ChartreuseK/Fennec6800_VTI/FennecVTI.kicad_sch

## KiCad design FennecVTI.kicad_sch (2023-05-26, an earlier design)

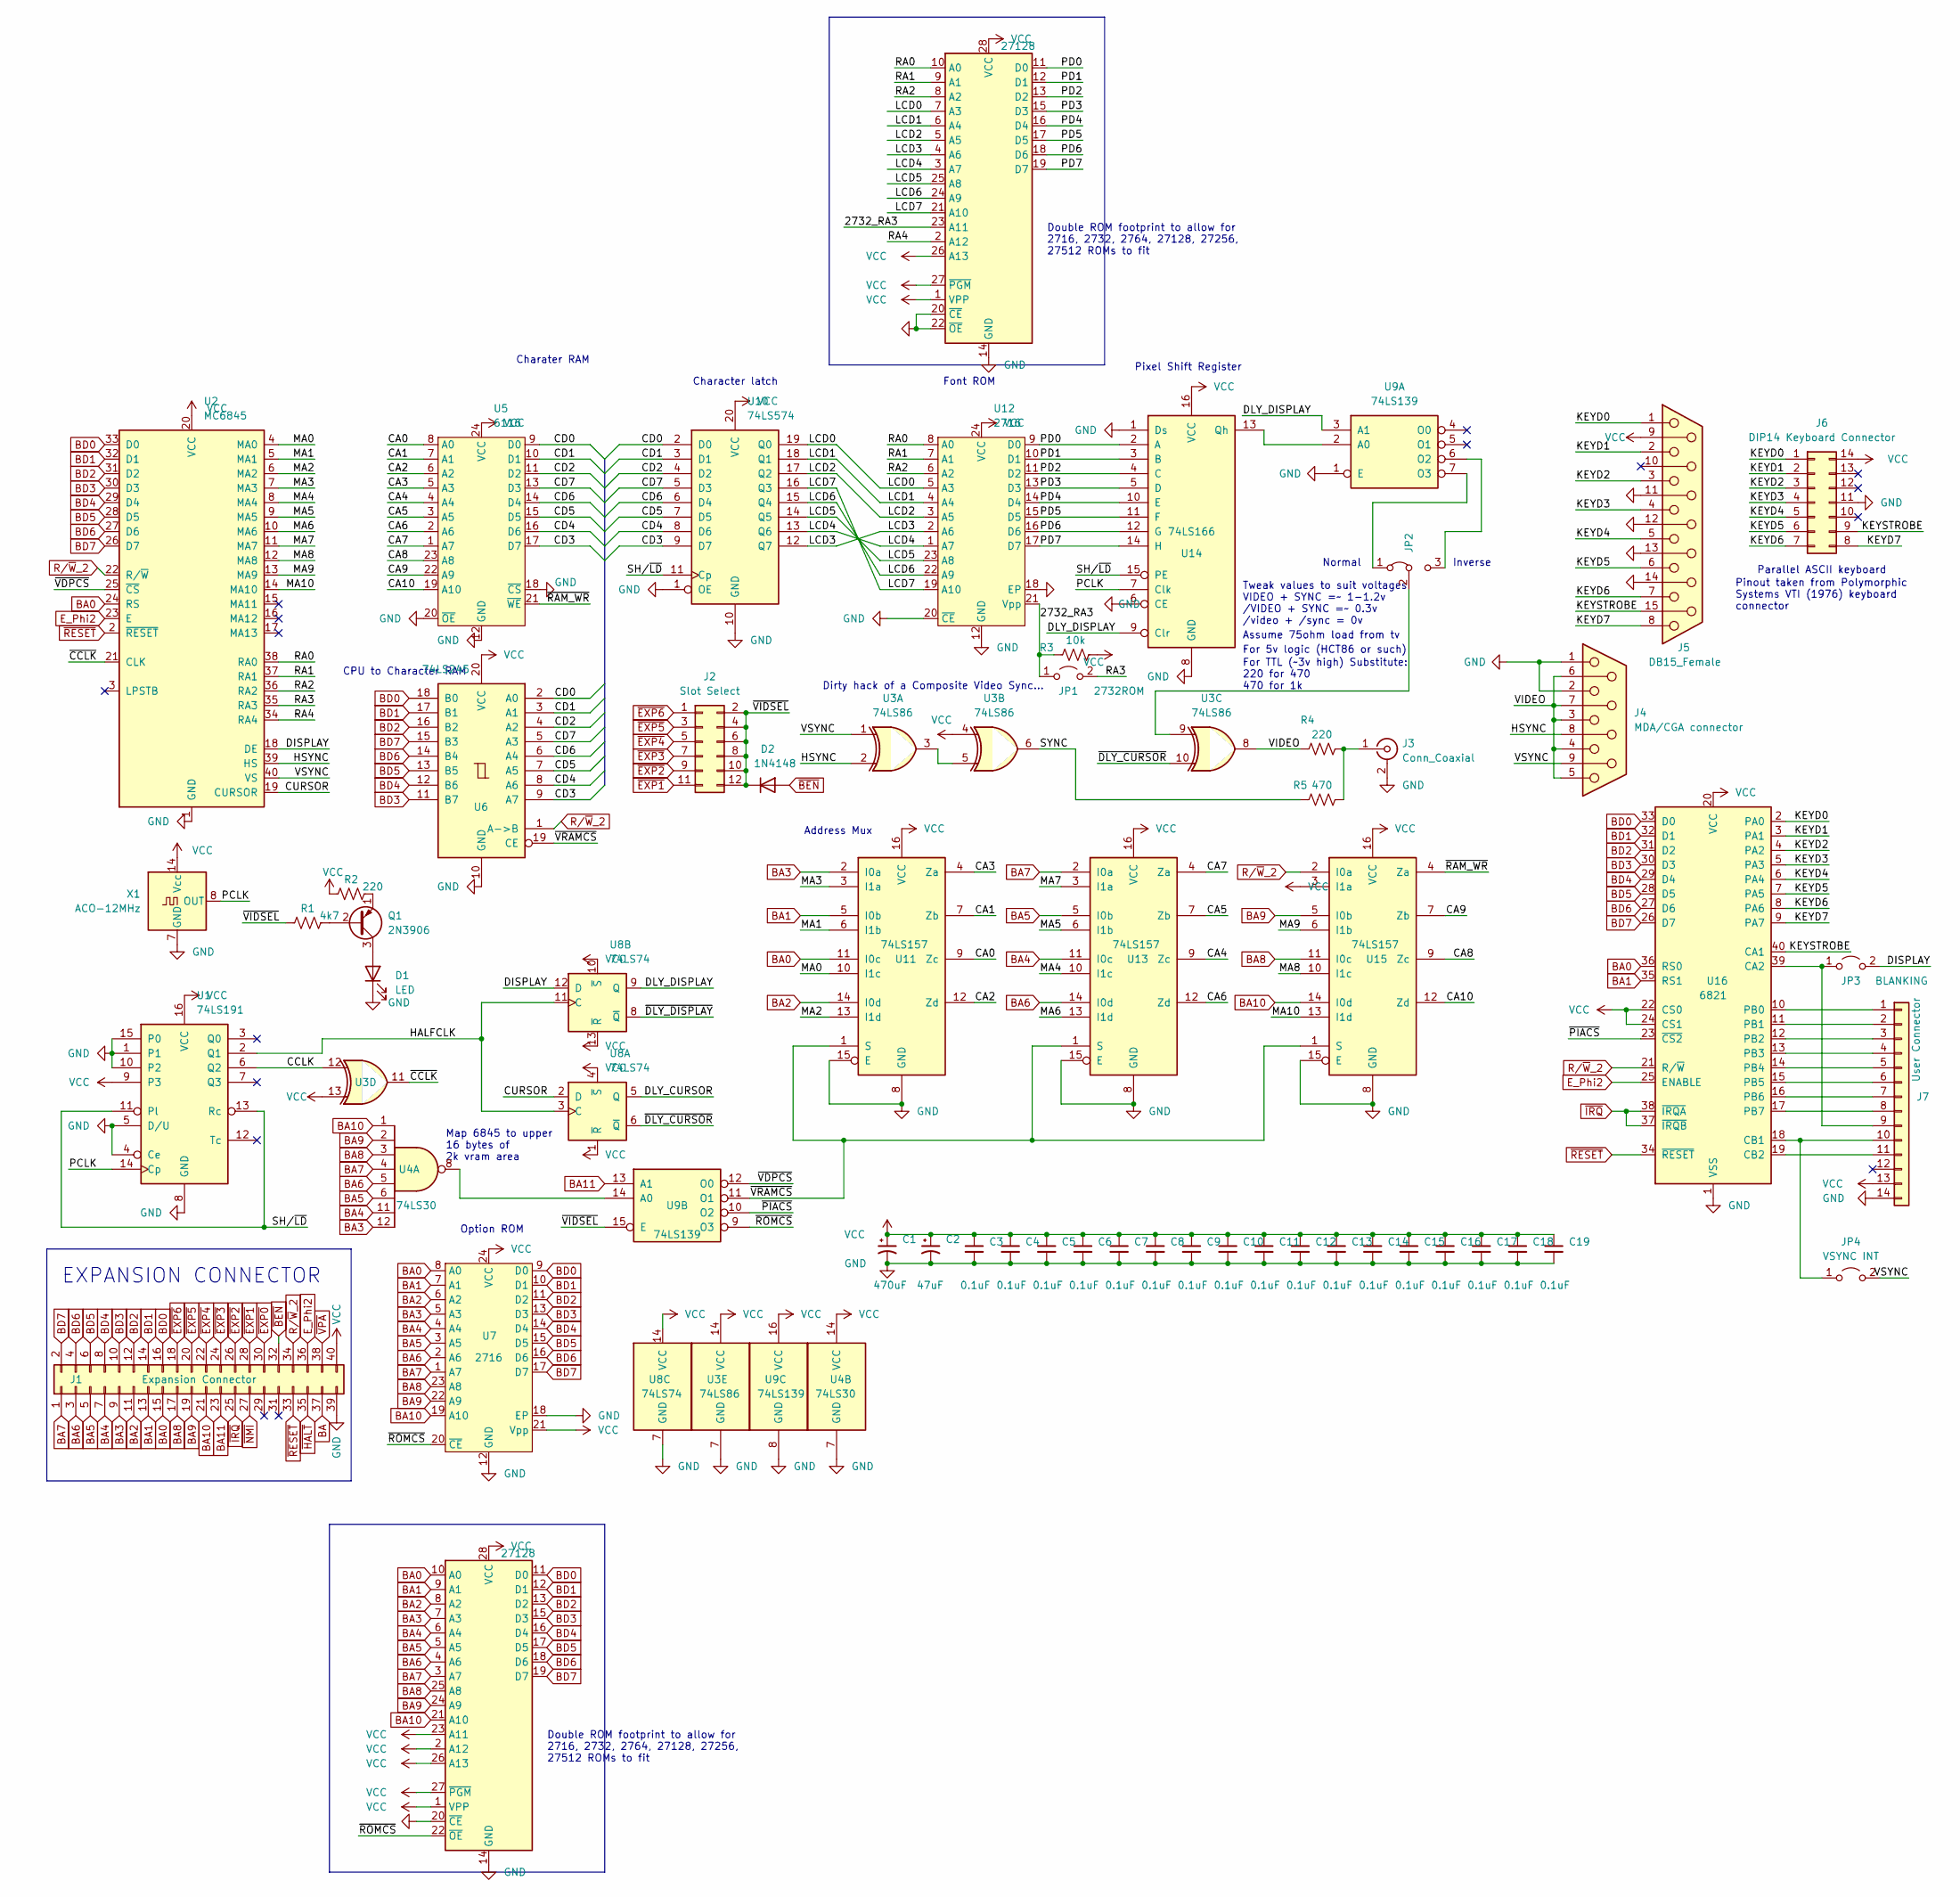
[picture p7: schematic FennecVTI.kicad_sch]

Parts:
C1: 470uF; CP_Radial_D8.0mm_P3.50mm
C2: 47uF; CP_Radial_D5.0mm_P2.00mm
C3, C4, C5, C6, C7, C8, C9, C10, C11, C12, C13, C14, C15, C16, C17, C18, C19: 0.1uF; C_Disc_D3.0mm_W1.6mm_P2.50mm
D1: LED; LED_D5.0mm
D2: 1N4148; D_DO-35_SOD27_P10.16mm_Horizontal
J1: Expansion Connector; PinHeader_2x20_P2.54mm_Vertical
J2: Slot Select; PinHeader_2x06_P2.54mm_Vertical
J3: Conn_Coaxial; RCA_RA_Switchcraft
J4: MDA/CGA connector; DSUB-9_Female_Horizontal_P2.77x2.84mm_EdgePinOffset7.70mm_H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
J5: DB15_Female; DSUB-15_Female_Horizontal_P2.77x2.84mm_EdgePinOffset7.70mm_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
J6: DIP14 Keyboard Connector; DIP-14_W7.62mm_Socket_LongPads
J7: User Connector; PinHeader_1x14_P2.54mm_Vertical
JP1: 2732ROM; PinHeader_1x02_P2.54mm_Vertical
JP2: Jumper_3_Bridged12; PinHeader_1x03_P2.54mm_Vertical
JP3: BLANKING; PinHeader_1x02_P2.54mm_Vertical
JP4: VSYNC INT; PinHeader_1x02_P2.54mm_Vertical
Q1: 2N3906; TO-92_Inline
R1: 4k7; R_Axial_DIN0207_L6.3mm_D2.5mm_P10.16mm_Horizontal
R2, R4: 220; R_Axial_DIN0207_L6.3mm_D2.5mm_P10.16mm_Horizontal
R3: 10k; R_Axial_DIN0207_L6.3mm_D2.5mm_P10.16mm_Horizontal
R5: 470; R_Axial_DIN0207_L6.3mm_D2.5mm_P10.16mm_Horizontal
U1: 74LS191; DIP-16 Copper Ref Pin 1 Mark
U2: MC6845; DIP-40 Copper Ref Pin 1
U3: 74LS86; DIP-14 Copper Ref Pin 1 Mark
U4: 74LS30; DIP-14 Copper Ref Pin 1 Mark
U5: 6116; DIP-24_W15.24mm_Socket_LongPads
U6: 74LS245; DIP-20 Copper Ref Pin 1 Mark
U7, U12: 2716; DIP-24_W15.24mm_Socket_LongPads
U8: 74LS74; DIP-14 Copper Ref Pin 1 Mark
U9: 74LS139; DIP-16 Copper Ref Pin 1 Mark
U10: 74LS574; DIP-20 Copper Ref Pin 1 Mark
U11, U13, U15: 74LS157; DIP-16 Copper Ref Pin 1 Mark
U14: 74LS166; DIP-16 Copper Ref Pin 1 Mark
U16: 6821; DIP-40 Copper Ref Pin 1
U70, U120: 27128; DIP-28_W15.24mm_Socket_LongPads
X1: ACO-12MHz; DIP-14-8 Crystal Silk Ref Pin 1 Outline

Connections:
2732_RA3: JP1.1 (A), R3.1, U12.21 (Vpp), U120.23 (A11)
BA: J1.37
BA0: J1.15, U2.24 (RS), U7.8 (A0), U11.11 (I0c), U16.36 (RS0), U70.10 (A0)
BA1: J1.13, U7.7 (A1), U11.5 (I0b), U16.35 (RS1), U70.9 (A1)
BA2: J1.11, U7.6 (A2), U11.14 (I0d), U70.8 (A2)
BA3: J1.9, U4.12, U7.5 (A3), U11.2 (I0a), U70.7 (A3)
BA4: J1.7, U4.11, U7.4 (A4), U13.11 (I0c), U70.6 (A4)
BA5: J1.5, U4.6, U7.3 (A5), U13.5 (I0b), U70.5 (A5)
BA6: J1.3, U4.5, U7.2 (A6), U13.14 (I0d), U70.4 (A6)
BA7: J1.1, U4.4, U7.1 (A7), U13.2 (I0a), U70.3 (A7)
BA8: J1.17, U4.3, U7.23 (A8), U15.11 (I0c), U70.25 (A8)
BA9: J1.19, U4.2, U7.22 (A9), U15.5 (I0b), U70.24 (A9)
BA10: J1.21, U4.1, U7.19 (A10), U15.14 (I0d), U70.21 (A10)
BA11: J1.23, U9.13 (A1)
BD0: J1.16, U2.33 (D0), U6.18 (B0), U7.9 (D0), U16.33 (D0), U70.11 (D0)
BD1: J1.14, U2.32 (D1), U6.17 (B1), U7.10 (D1), U16.32 (D1), U70.12 (D1)
BD2: J1.12, U2.31 (D2), U6.16 (B2), U7.11 (D2), U16.31 (D2), U70.13 (D2)
BD3: J1.10, U2.30 (D3), U6.11 (B7), U7.13 (D3), U16.30 (D3), U70.15 (D3)
BD4: J1.8, U2.29 (D4), U6.12 (B6), U7.14 (D4), U16.29 (D4), U70.16 (D4)
BD5: J1.6, U2.28 (D5), U6.13 (B5), U7.15 (D5), U16.28 (D5), U70.17 (D5)
BD6: J1.4, U2.27 (D6), U6.14 (B4), U7.16 (D6), U16.27 (D6), U70.18 (D6)
BD7: J1.2, U2.26 (D7), U6.15 (B3), U7.17 (D7), U16.26 (D7), U70.19 (D7)
CA0: U5.8 (A0), U11.9 (Zc)
CA1: U5.7 (A1), U11.7 (Zb)
CA2: U5.6 (A2), U11.12 (Zd)
CA3: U5.5 (A3), U11.4 (Za)
CA4: U5.4 (A4), U13.9 (Zc)
CA5: U5.3 (A5), U13.7 (Zb)
CA6: U5.2 (A6), U13.12 (Zd)
CA7: U5.1 (A7), U13.4 (Za)
CA8: U5.23 (A8), U15.9 (Zc)
CA9: U5.22 (A9), U15.7 (Zb)
CA10: U5.19 (A10), U15.12 (Zd)
CCLK: U1.6 (Q2), U3.12
CD0: U5.9 (D0), U6.2 (A0), U10.2 (D0)
CD1: U5.10 (D1), U6.3 (A1), U10.3 (D1)
CD2: U5.11 (D2), U6.4 (A2), U10.4 (D2)
CD3: U5.17 (D7), U6.9 (A7), U10.9 (D7)
CD4: U5.16 (D6), U6.8 (A6), U10.8 (D6)
CD5: U5.15 (D5), U6.7 (A5), U10.7 (D5)
CD6: U5.14 (D4), U6.6 (A4), U10.6 (D4)
CD7: U5.13 (D3), U6.5 (A3), U10.5 (D3)
CURSOR: U2.19 (CURSOR), U8.2 (D)
DISPLAY: JP3.2 (B), U2.18 (DE), U8.12 (D)
DLY_CURSOR: U8.5 (Q)
DLY_DISPLAY: U8.9 (Q), U9.3 (A1), U14.9 (Clr)
E_Phi2: J1.36, U2.23 (E), U16.25 (ENABLE)
GND: C1.2, C2.2, C3.2, C4.2, C5.2, C6.2, C7.2, C8.2, C9.2, C10.2, C11.2, C12.2, C13.2, C14.2, C15.2, C16.2, C17.2, C18.2, C19.2, D1.1 (K), J1.39, J3.2 (Ext), J4.1, J4.2, J5.11 (P111), J5.12, J5.13, J5.14, J6.11, J7.14, U1.1, U1.4 (Ce), U1.5 (D/U), U1.8 (GND), U1.10 (P2), U1.15 (P0), U2.1 (GND), U3.7 (GND), U4.7 (GND), U5.12 (GND), U5.18 (~CS), U5.20 (~OE), U6.10 (GND), U7.12 (GND), U7.18 (EP), U8.7 (GND), U9.1 (E), U9.8 (GND), U10.1 (OE), U10.10 (GND), U11.8 (GND), U11.15 (E), U12.12 (GND), U12.18 (EP), U12.20 (~CE), U13.8 (GND), U13.15 (E), U14.1 (Ds), U14.6 (CE), U14.8 (GND), U15.8 (GND), U15.15 (E), U16.1 (VSS), U70.14 (GND), U70.20 (~CE), U120.14 (GND), U120.20 (~CE), U120.22 (~OE), X1.7 (GND)
HALFCLK: U1.2 (Q1), U8.3 (C), U8.11 (C)
HSYNC: J4.8, U2.39 (HS), U3.2
KEYD0: J5.1, J6.1, U16.2 (PA0)
KEYD1: J5.2, J6.2, U16.3 (PA1)
KEYD2: J5.3, J6.3, U16.4 (PA2)
KEYD3: J5.4, J6.4, U16.5 (PA3)
KEYD4: J5.5, J6.5, U16.6 (PA4)
KEYD5: J5.6, J6.6, U16.7 (PA5)
KEYD6: J5.7, J6.7, U16.8 (PA6)
KEYD7: J5.8, J6.8, U16.9 (PA7)
KEYSTROBE: J5.15, J6.9, U16.40 (CA1)
LCD0: U10.19 (Q0), U12.5 (A3), U120.7 (A3)
LCD1: U10.18 (Q1), U12.4 (A4), U120.6 (A4)
LCD2: U10.17 (Q2), U12.3 (A5), U120.5 (A5)
LCD3: U10.12 (Q7), U12.2 (A6), U120.4 (A6)
LCD4: U10.13 (Q6), U12.1 (A7), U120.3 (A7)
LCD5: U10.14 (Q5), U12.23 (A8), U120.25 (A8)
LCD6: U10.15 (Q4), U12.22 (A9), U120.24 (A9)
LCD7: U10.16 (Q3), U12.19 (A10), U120.21 (A10)
MA0: U2.4 (MA0), U11.10 (I1c)
MA1: U2.5 (MA1), U11.6 (I1b)
MA2: U2.6 (MA2), U11.13 (I1d)
MA3: U2.7 (MA3), U11.3 (I1a)
MA4: U2.8 (MA4), U13.10 (I1c)
MA5: U2.9 (MA5), U13.6 (I1b)
MA6: U2.10 (MA6), U13.13 (I1d)
MA7: U2.11 (MA7), U13.3 (I1a)
MA8: U2.12 (MA8), U15.10 (I1c)
MA9: U2.13 (MA9), U15.6 (I1b)
MA10: U2.14 (MA10), U15.13 (I1d)
unnamed: D1.2 (A), Q1.3 (C)
unnamed: J3.1 (In), R4.2, R5.2
unnamed: J7.1, U16.10 (PB0)
unnamed: J7.2, U16.11 (PB1)
unnamed: J7.3, U16.12 (PB2)
unnamed: J7.4, U16.13 (PB3)
unnamed: J7.5, U16.14 (PB4)
unnamed: J7.6, U16.15 (PB5)
unnamed: J7.7, U16.16 (PB6)
unnamed: J7.8, U16.17 (PB7)
unnamed: J7.9, JP3.1 (A), U16.39 (CA2)
unnamed: J7.10, JP4.1 (A), U16.18 (CB1)
unnamed: J7.11, U16.19 (CB2)
unnamed: JP2.1 (A), U9.7 (O3)
unnamed: JP2.2 (C), U3.9
unnamed: JP2.3 (B), U9.6 (O2)
unnamed: Q1.1 (E), R2.2
unnamed: Q1.2 (B), R1.2
unnamed: U3.3, U3.5
unnamed: U4.8, U9.14 (A0)
unnamed: U9.2 (A0), U14.13 (Qh)
PCLK: U1.14 (Cp), U14.7 (Clk), X1.8 (OUT)
PD0: U12.9 (D0), U14.2 (A), U120.11 (D0)
PD1: U12.10 (D1), U14.3 (B), U120.12 (D1)
PD2: U12.11 (D2), U14.4 (C), U120.13 (D2)
PD3: U12.13 (D3), U14.5 (D), U120.15 (D3)
PD4: U12.14 (D4), U14.10 (E), U120.16 (D4)
PD5: U12.15 (D5), U14.11 (F), U120.17 (D5)
PD6: U12.16 (D6), U14.12 (G), U120.18 (D6)
PD7: U12.17 (D7), U14.14 (H), U120.19 (D7)
RA0: U2.38 (RA0), U12.8 (A0), U120.10 (A0)
RA1: U2.37 (RA1), U12.7 (A1), U120.9 (A1)
RA2: U2.36 (RA2), U12.6 (A2), U120.8 (A2)
RA3: JP1.2 (B), U2.35 (RA3)
RA4: U2.34 (RA4), U120.2 (A12)
R/~W_2: J1.34, U2.22 (R/~W), U6.1 (A->B), U15.2 (I0a), U16.21 (R/~W)
SH/~LD: U1.11 (Pl), U1.13 (Rc), U10.11 (Cp), U14.15 (PE)
SYNC: R5.1, U3.6
VCC: C1.1, C2.1, C3.1, C4.1, C5.1, C6.1, C7.1, C8.1, C9.1, C10.1, C11.1, C12.1, C13.1, C14.1, C15.1, C16.1, C17.1, C18.1, C19.1, J1.40, J5.9, J6.14, J7.13, R2.1, R3.2, U1.9 (P3), U1.16 (VCC), U2.20 (VCC), U3.4, U3.13, U3.14 (VCC), U4.14 (VCC), U5.24 (VCC), U6.20 (VCC), U7.21 (Vpp), U7.24 (VCC), U8.1 (~R), U8.4 (~S), U8.10 (~S), U8.13 (~R), U8.14 (VCC), U9.16 (VCC), U10.20 (VCC), U11.16 (VCC), U12.24 (VCC), U13.16 (VCC), U14.16 (VCC), U15.3 (I1a), U15.16 (VCC), U16.20 (VCC), U16.22 (CS0), U16.24 (CS1), U70.1 (VPP), U70.2 (A12), U70.23 (A11), U70.26 (A13), U70.27 (~PGM), U70.28 (VCC), U120.1 (VPP), U120.26 (A13), U120.27 (~PGM), U120.28 (VCC), X1.14 (Vcc)
VIDEO: J4.3, J4.4, J4.5, J4.6, J4.7, R4.1, U3.8
VSYNC: J4.9, JP4.2 (B), U2.40 (VS), U3.1
~BEN: D2.2 (A), J1.32
~CCLK: U2.21 (CLK), U3.11
~DLY_CURSOR: U3.10, U8.6 (~Q)
~DLY_DISPLAY: U8.8 (~Q)
~EXP0: J1.30
~EXP1: J1.28, J2.11
~EXP2: J1.26, J2.9
~EXP3: J1.24, J2.7
~EXP4: J1.22, J2.5
~EXP5: J1.20, J2.3
~EXP6: J1.18, J2.1
~HALT: J1.35
~IRQ: J1.25, U16.37 (~IRQB), U16.38 (~IRQA)
~NMI: J1.27
~PIACS: U9.10 (O2), U16.23 (~CS2)
~RAM_WR: U5.21 (~WE), U15.4 (Za)
~RESET: J1.33, U2.2 (~RESET), U16.34 (~RESET)
~ROMCS: U7.20 (~CE), U9.9 (O3), U70.22 (~OE)
~VDPCS: U2.25 (~CS), U9.12 (O0)
~VIDSEL: D2.1 (K), J2.2, J2.4, J2.6, J2.8, J2.10, J2.12, R1.1, U9.15 (E)
~VPA: J1.38
~VRAMCS: U6.19 (CE), U9.11 (O1), U11.1 (S), U13.1 (S), U15.1 (S)

Notes on the sheet:
Normal
Double ROM footprint to allow for 2716, 2732, 2764, 27128, 27256, 27512 ROMs to fit
Address Mux
Pixel Shift Register
For TTL (~3v high) Substitute: 220 for 470 470 for 1k
EXPANSION CONNECTOR
Map 6845 to upper 16 bytes of 2k vram area
For 5v logic (HCT86 or such)
Dirty hack of a Composite Video Sync...
Option ROM
Tweak values to suit voltages VIDEO + SYNC =~ 1-1.2v /VIDEO + SYNC =~ 0.3v /video + /sync = 0v
CPU to Character RAM
Charater RAM
Pinout taken from Polymorphic Systems VTI (1976) keyboard connector
Character latch
Inverse
Parallel ASCII keyboard
Font ROM
Assume 75ohm load from tv
